phastmike/neutec-repeater-hardware/CT1ENQ_CT1EYN/bottom/Export/1.0/RepeaterController3D_V1.0_Top.png

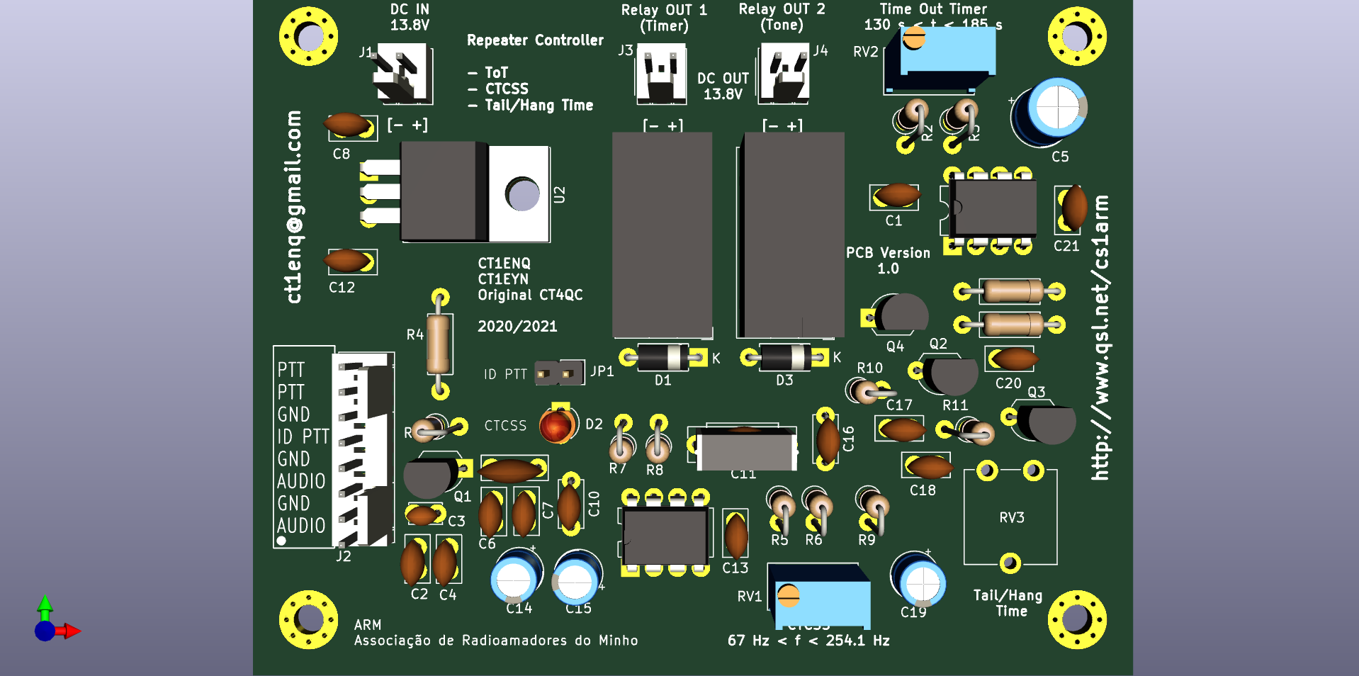
CT1ENQ_CT1EYN/bottom/Export/1.0/RepeaterController3D_V1.0_Top.png
