phastmike/neutec-repeater-hardware/CT1ENQ_CT1EYN/top/Export/1.0/alfa/RepeaterController_3d_1.jpg

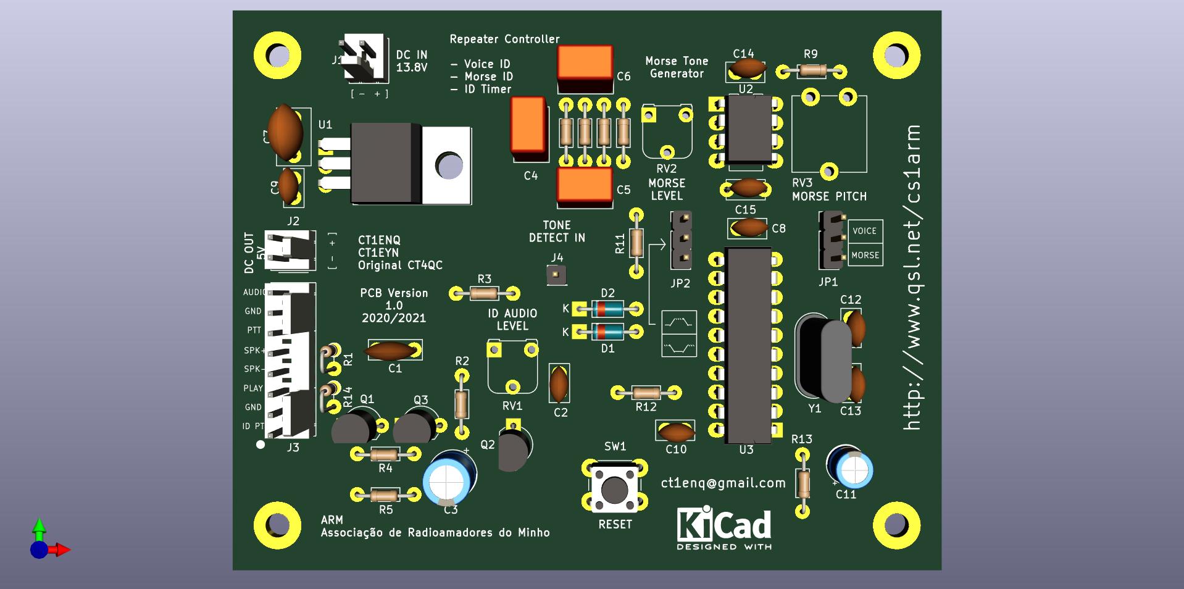
CT1ENQ_CT1EYN/top/Export/1.0/alfa/RepeaterController_3d_1.jpg
