phastmike/neutec-repeater-hardware/CT1ENQ_CT1EYN/bottom/Export/1.1/RepeaterController_1_1_BW.pdf

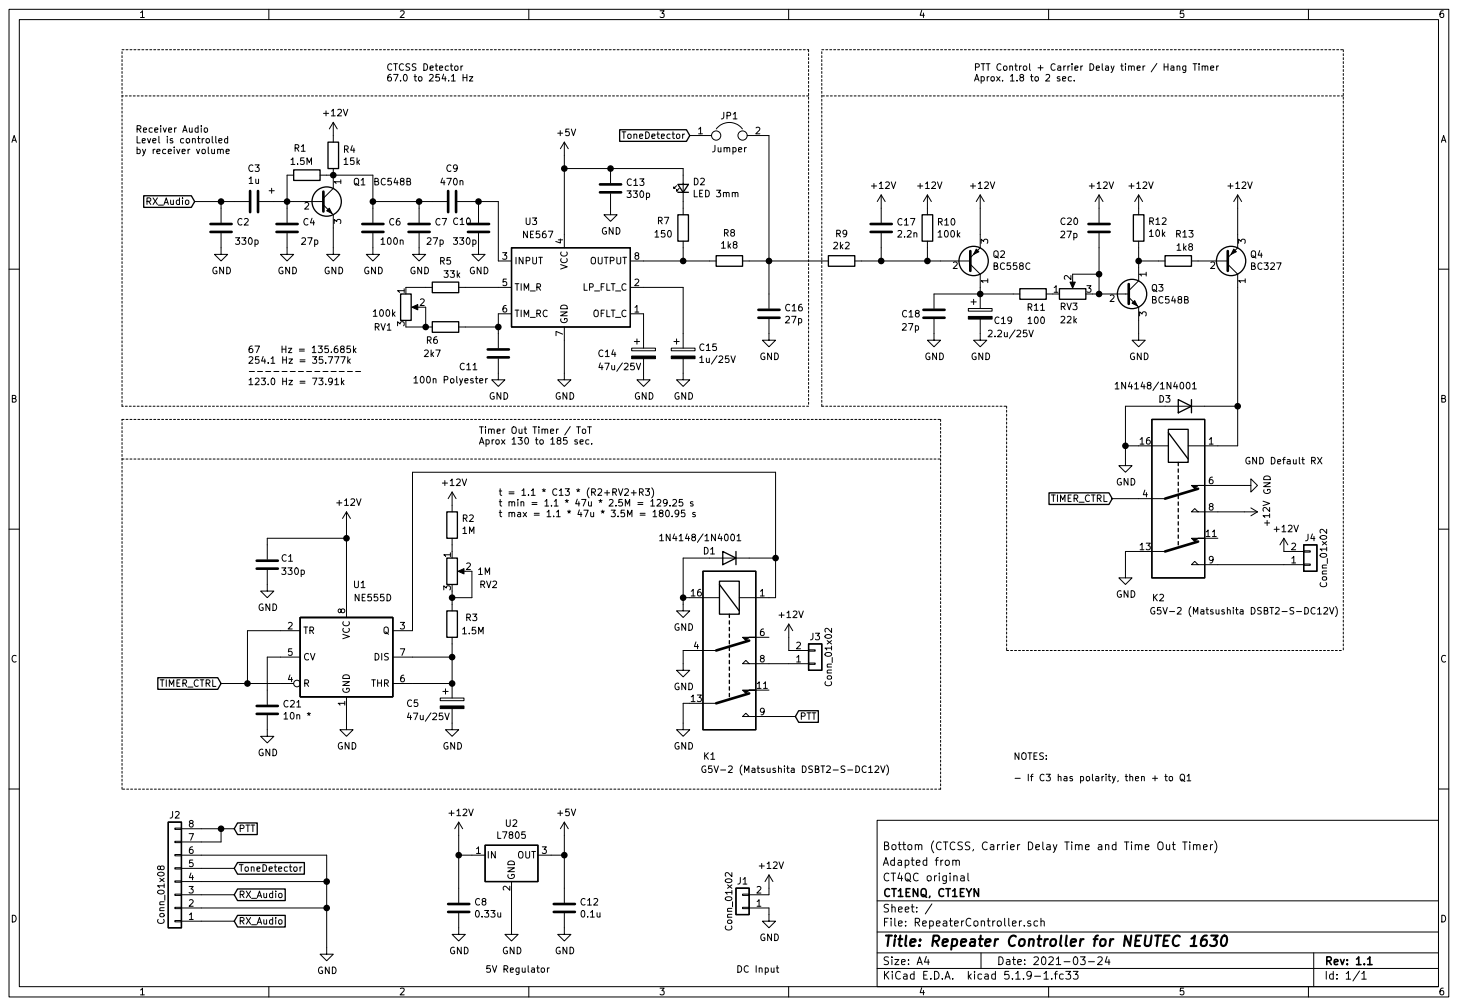
[picture p20: page 1]

PTT Control + Carrier Delay timer / Hang Timer

3 Q1 BC548B GND GND GND GND

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

Id: 1/1 Title: Repeater Controller for NEUTEC 1630
