phastmike/neutec-repeater-hardware/CT1ENQ_CT1EYN/top/Export/1.0/alfa/RepeaterController-F_SilkS_Invertido.pdf

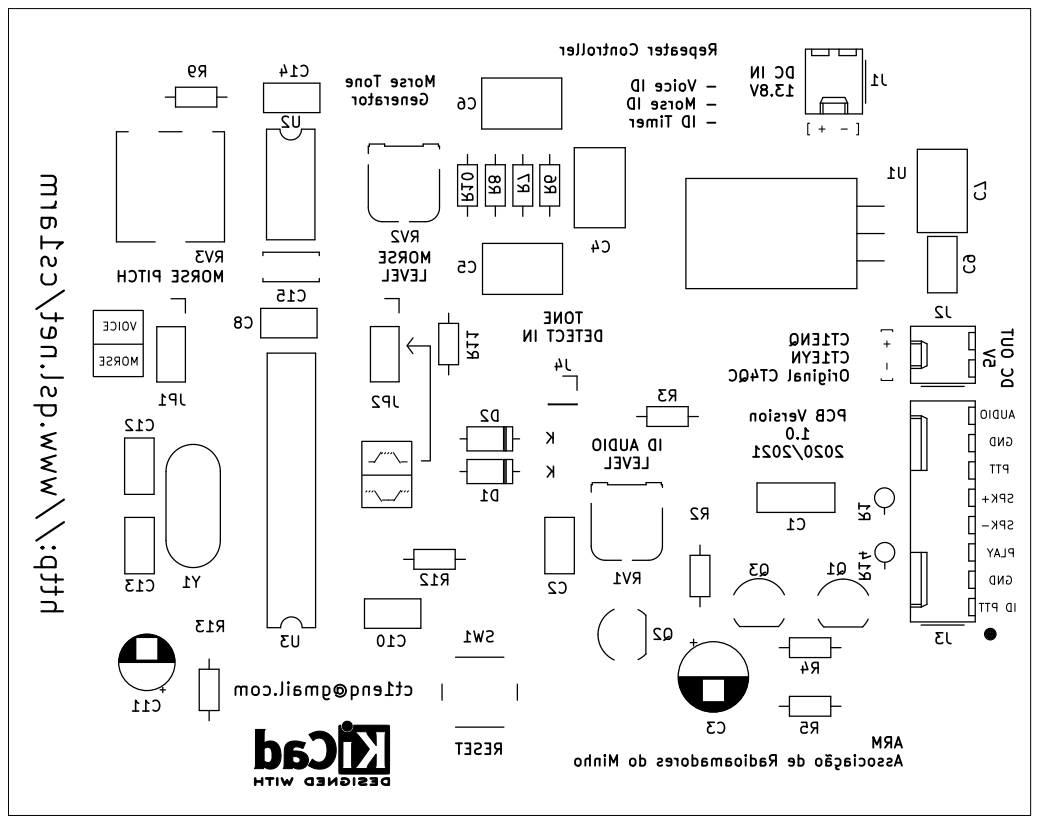
[picture p21: page 1]

Morse Tone Generator ct1enq@gmail.com

VOICE TONE DETECT IN http://www.qsl.net/cs1arm

LEVEL MORSE PITCH MORSE

Associação de Radioamadores do Minho CT1ENQ

SPK- SPK+ PTT GND GND
