phastmike/neutec-repeater-hardware/CT1ENQ_CT1EYN/top/Export/1.0/alfa/RepeaterController-F_SilkS_Normal.pdf

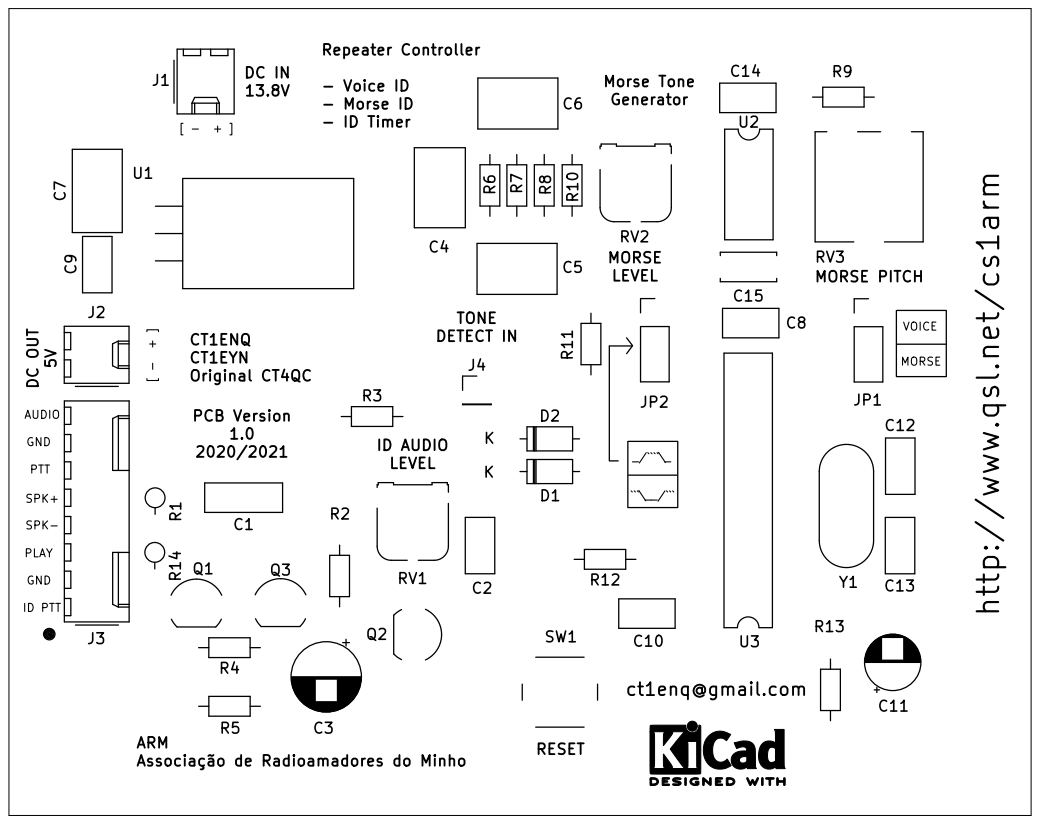
[picture p22: page 1]

LEVEL DC IN
Morse Tone Generator ct1enq@gmail.com

Associação de Radioamadores do Minho CT1ENQ

SPK- SPK+ PTT GND GND
