phastmike/neutec-repeater-hardware/CT1ENQ_CT1EYN/top/Export/1.0/beta/RepeaterController-F_SilkS_Normal.pdf

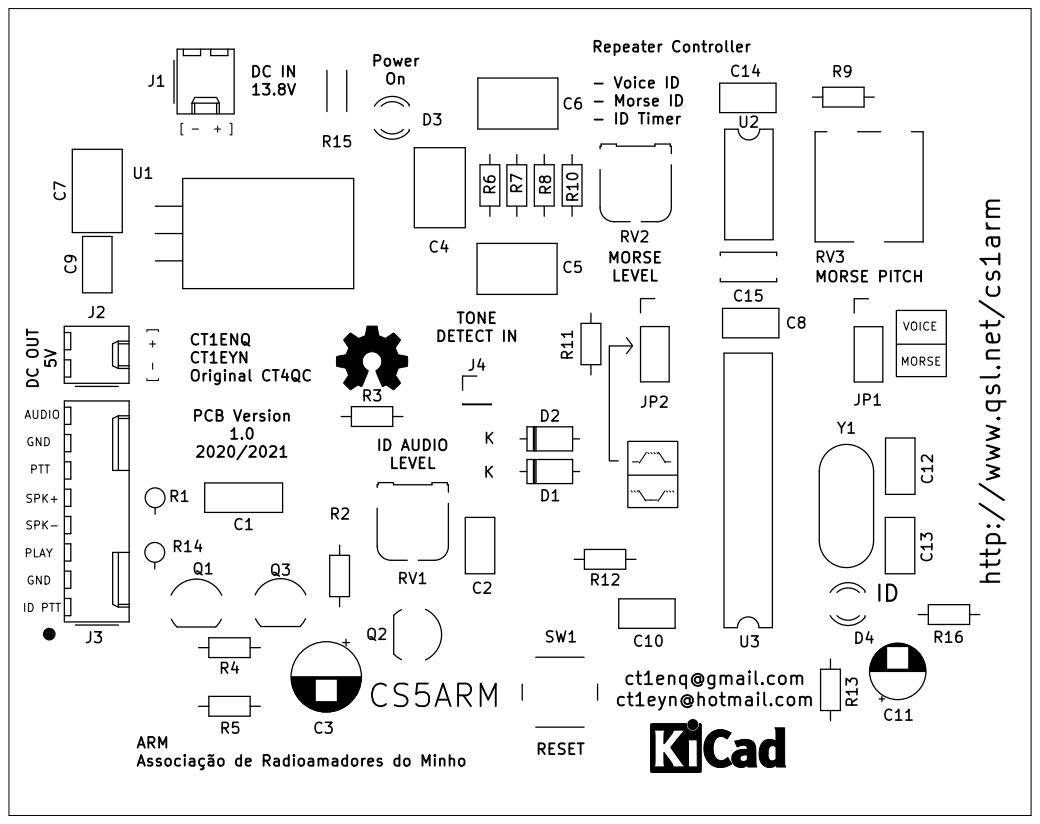
[picture p23: page 1]

Associação de Radioamadores do Minho CT1ENQ

SPK- SPK+ PTT GND GND
