phastmike/neutec-repeater-hardware/CT1ENQ_CT1EYN/top/Export/1.0/beta/RepeaterController_BW.pdf

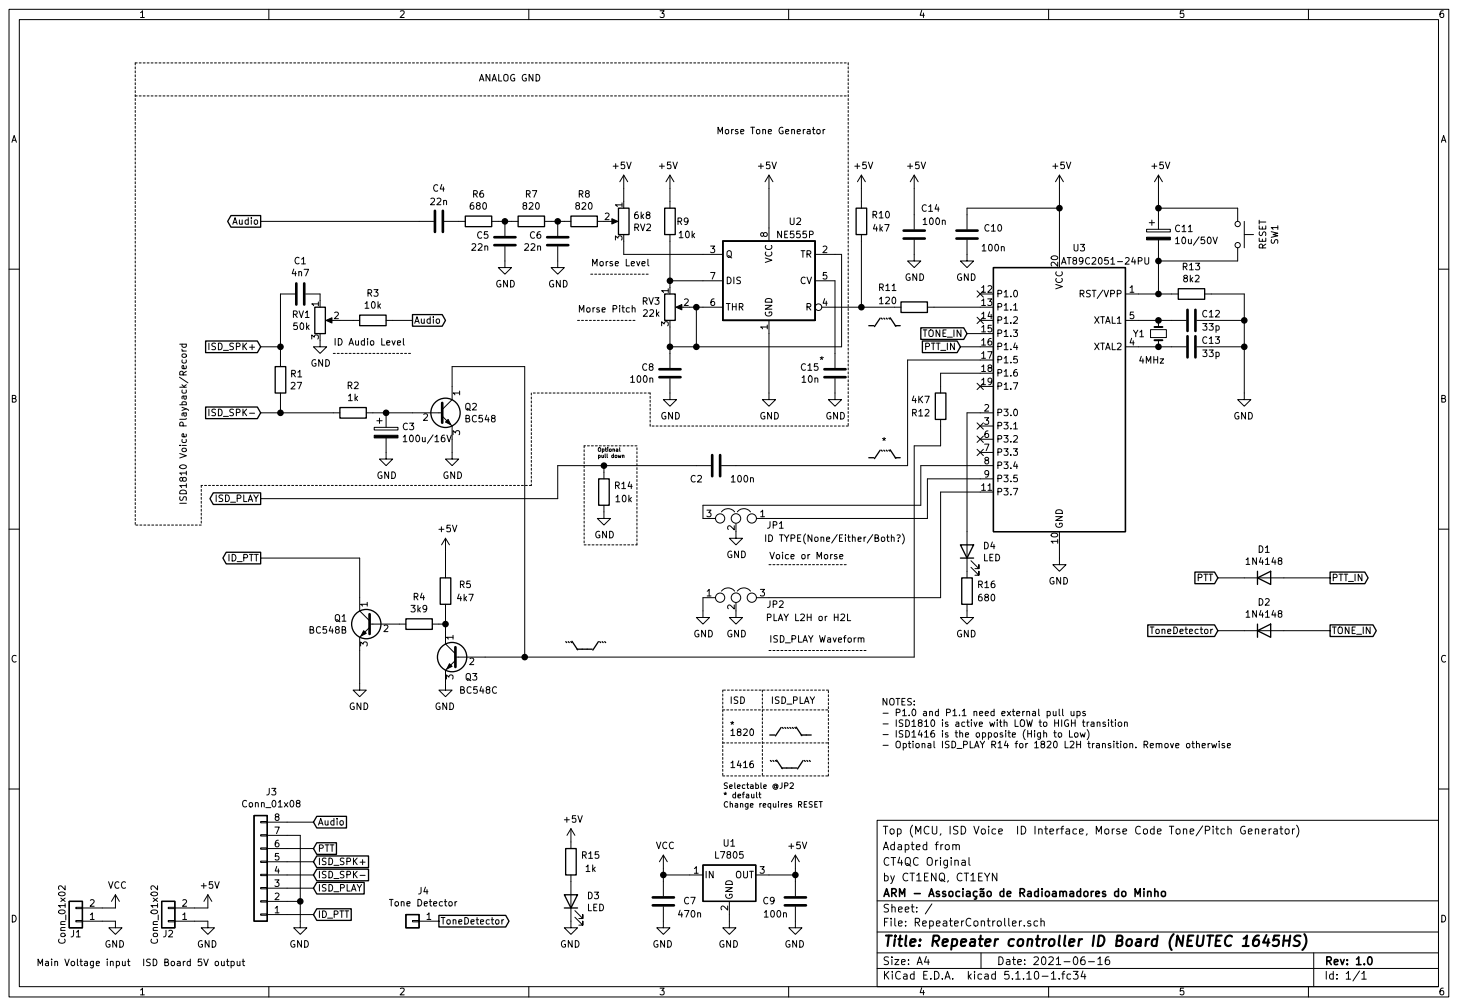
[picture p24: page 1]

- Optional ISD_PLAY R14 for 1820 L2H transition. Remove otherwise Morse Pitch

ISD_PLAY Waveform ISD1810 Voice Playback/Record

Top (MCU, ISD Voice ID Interface, Morse Code Tone/Pitch Generator) GND

ID TYPE(None/Either/Both?) R14

JP2 PLAY L2H or H2L GND GND

ISD ISD_PLAY

- ISD1810 is active with LOW to HIGH transition - ISD1416 is the opposite (High to Low)

* default Change requires RESET

Adapted from
CT4QC Original
by CT1ENQ, CT1EYN
File: RepeaterController.sch Sheet: / ARM - Associação de Radioamadores do Minho

Id: 1/1 Title: Repeater controller ID Board (NEUTEC 1645HS)
