phastmike/neutec-repeater-hardware/CT1ENQ_CT1EYN/bottom/Export/1.1/RepeaterController-B_Cu.pdf

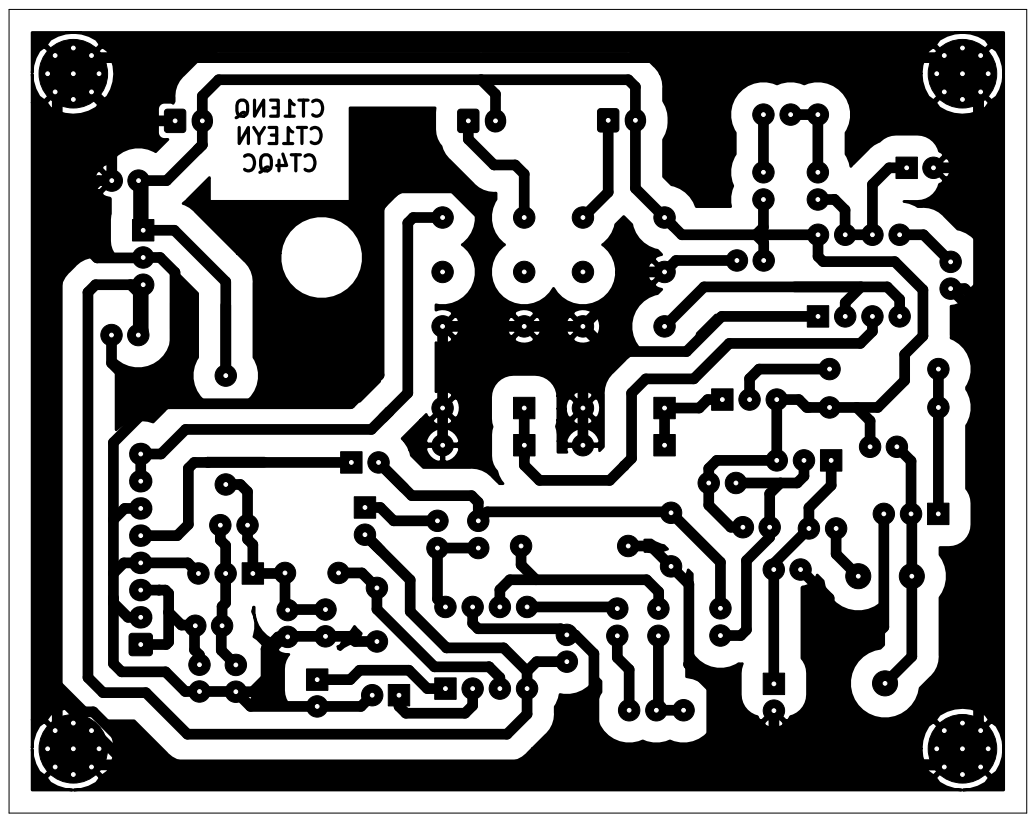
[picture p28: page 1]
