phastmike/neutec-repeater-hardware/CT1ENQ_CT1EYN/top/Export/1.0/alfa/RepeaterController-B_Cu.pdf

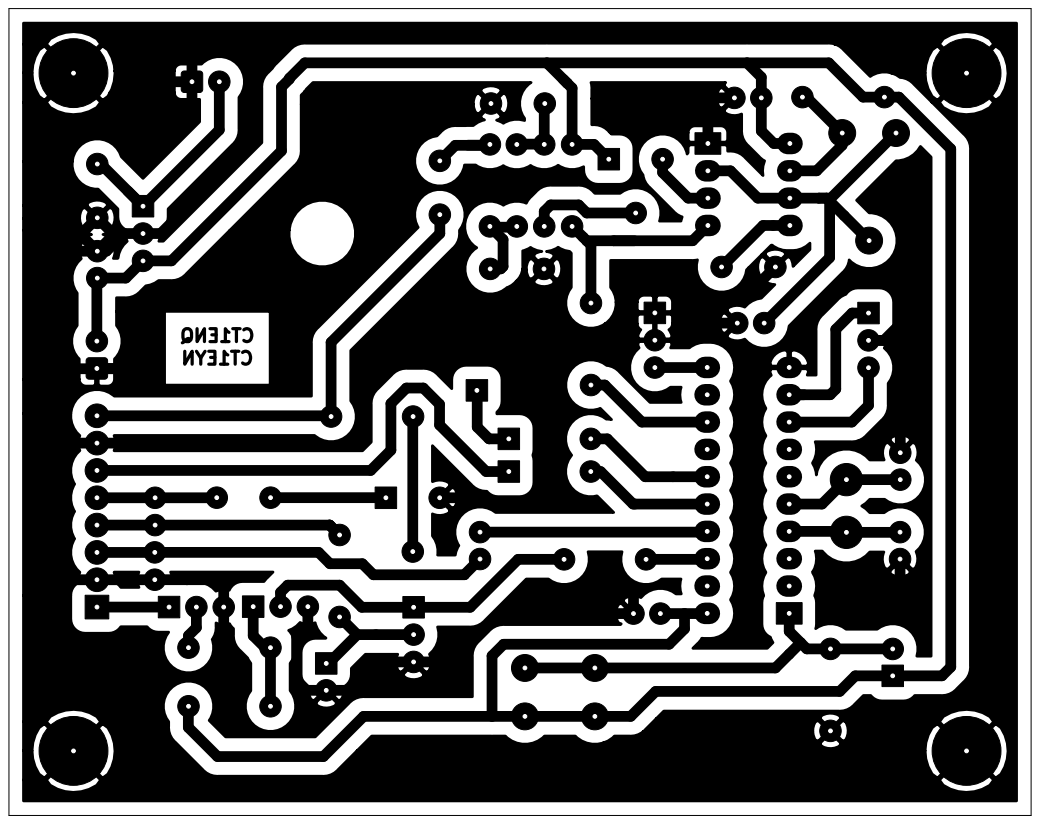
[picture p29: page 1]
