phastmike/neutec-repeater-hardware/CT1ENQ_CT1EYN/top/Export/1.0/beta/RepeaterController-B_Cu_Invertido.pdf

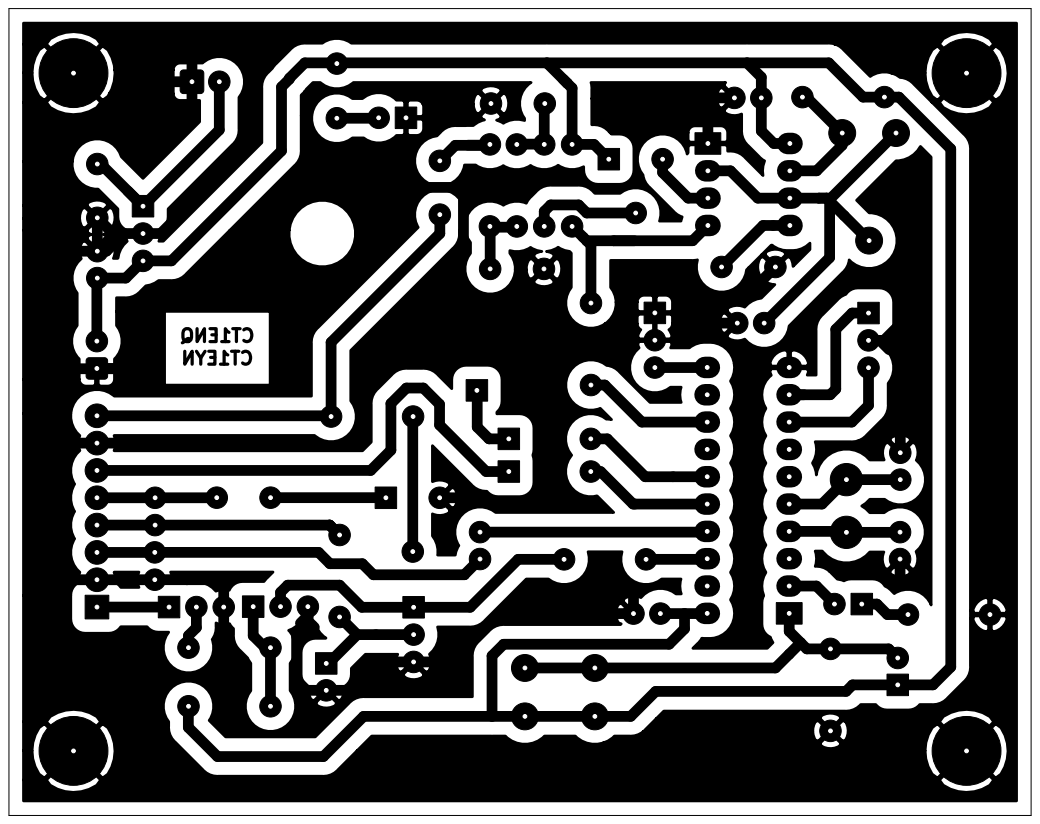
[picture p30: page 1]
