phastmike/neutec-repeater-hardware/CT1ENQ_CT1EYN/top/Export/1.0/beta/RepeaterController-B_Cu_Normal.pdf

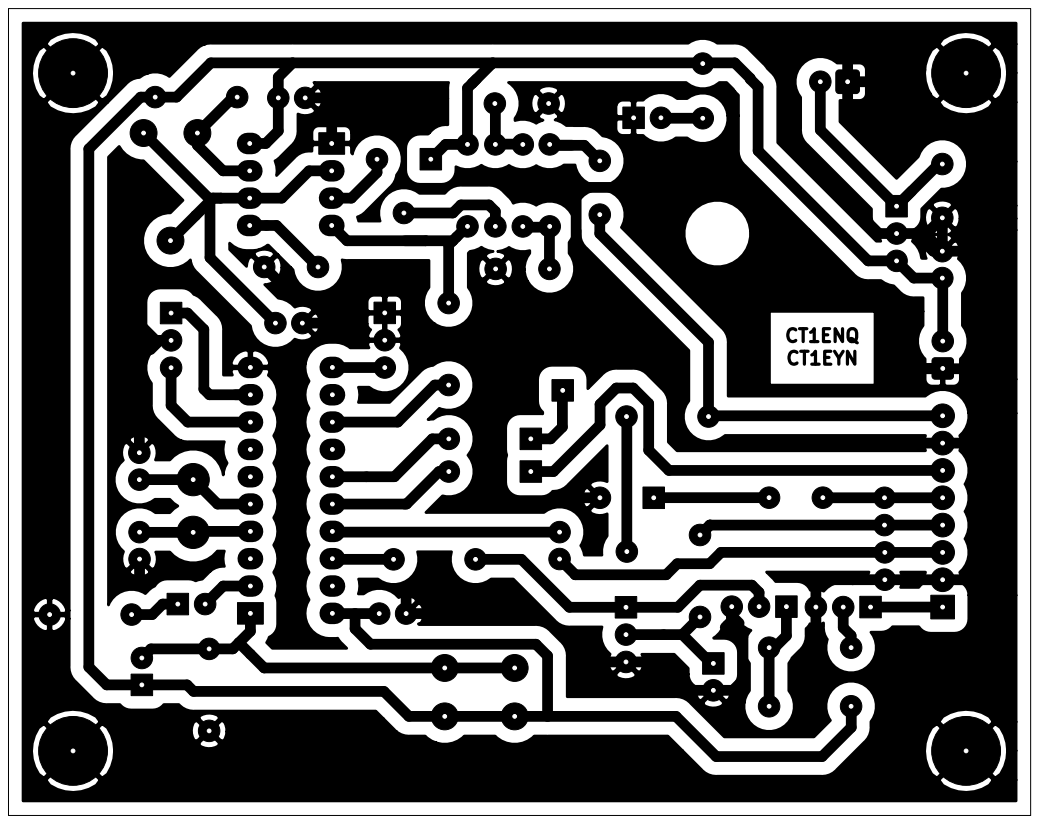
[picture p31: page 1]
