phastmike/neutec-repeater-hardware/CT4QC/mod/RepeaterController.sch

## KiCad design CT4QC/mod/RepeaterController.sch (2021-07-06)

Schematic: RepeaterController.sch

Parts:
C1, C2: 22n (0.022u)
C3: 22n
C4, C202: 100n
C5, C7, C8: 33p
C6: 10u/50V
C19: 4n7
C20: 100u/16V
C21: 150n
C201: 150n (u15)
D1: 1N4148
JP1: Dual Jumper
Q1: BC548B; TO-92_Inline
Q2: BC548C; TO-92_Inline
Q5: BC548; TO-92_Inline
R1, R2, R3: 820
R4, R17: 10k
R5: 3k9
R6, R10: 4k7
R7: 120
R8: 4K7
R9: 8k2
R15: 27
R16: 1k
RV1: 6k8
RV2: 50k
RV3: 22k
SW1: SW_Push_Dual
U1: L7805
U2: AT89C2051-24PU; DIP-20_W7.62mm
U3: NE555P; DIP-8_W7.62mm
Y1: 4MHz

Notes on the sheet:
ISD1416P Voice Playback/Record
Morse Tone Generator - Disabled -
NOTES: - Reset button is not being reused (June 2021)
Tone Freq.
Tone Level
