phastmike/neutec-repeater-hardware/CT4QC/original/bottom/RepeaterController.sch

## KiCad design CT4QC/original/bottom/RepeaterController.sch (2021-07-08)

Schematic: RepeaterController.sch

Parts:
C1: 330p (331J)
C2, C11: 1u
C3: 27pF (270K)
C4, C8: 100n
C5, C16, C18: 27p
C6: 470n (.47u)
C7, C9, C14: 330p
C10, C13: 47u/25V
C12: 27p (270K)
C15: 2.2n
C17: 2.2u
D1: 1N4148
D2: D
J1: Conn_01x07
K1, K2: RSM822; Relay_DPDT_Finder_40.52
Q1, Q3: BC548B; TO-92_Inline
Q2: BC558C; TO-92_Inline
Q4: BC327; TO-92_Inline
R1, R9: 1.5M
R2: 15k
R3, R11: 100k
R4, R13: 10k
R5, R14: 1k8
R7: 1M
R8: 330k
R10: 2k2
R12: 22k
RV1: 100k (31k)
U1: NE567
U2: NE555D; SOIC-8_3.9x4.9mm_P1.27mm

Notes on the sheet:
f = 1 / (1.1 * (R3 + RV1 + R4) * C8) f = 1 / (1,1 * (100k+31k + 10k) * 100n) f = 1 / (1,1 * 141k * 100n) f = ~ 64,5Hz (67Hz)
Receiver Audio Level is controlled by receiver volume
Radio J201 Connector
t = 1.1 * C13 * (R7+R8+R9) t = 1.1 * 47u * 2.83M = 146,311 s
Tone Detector
Output
(104K)
NOTES: - 5V comes from regulator in the radio (near front panel)
